Stwikey/alien-kitty/schematic/alienkitty.kicad_sch

## KiCad design schematic/alienkitty.kicad_sch (2026-06-14)

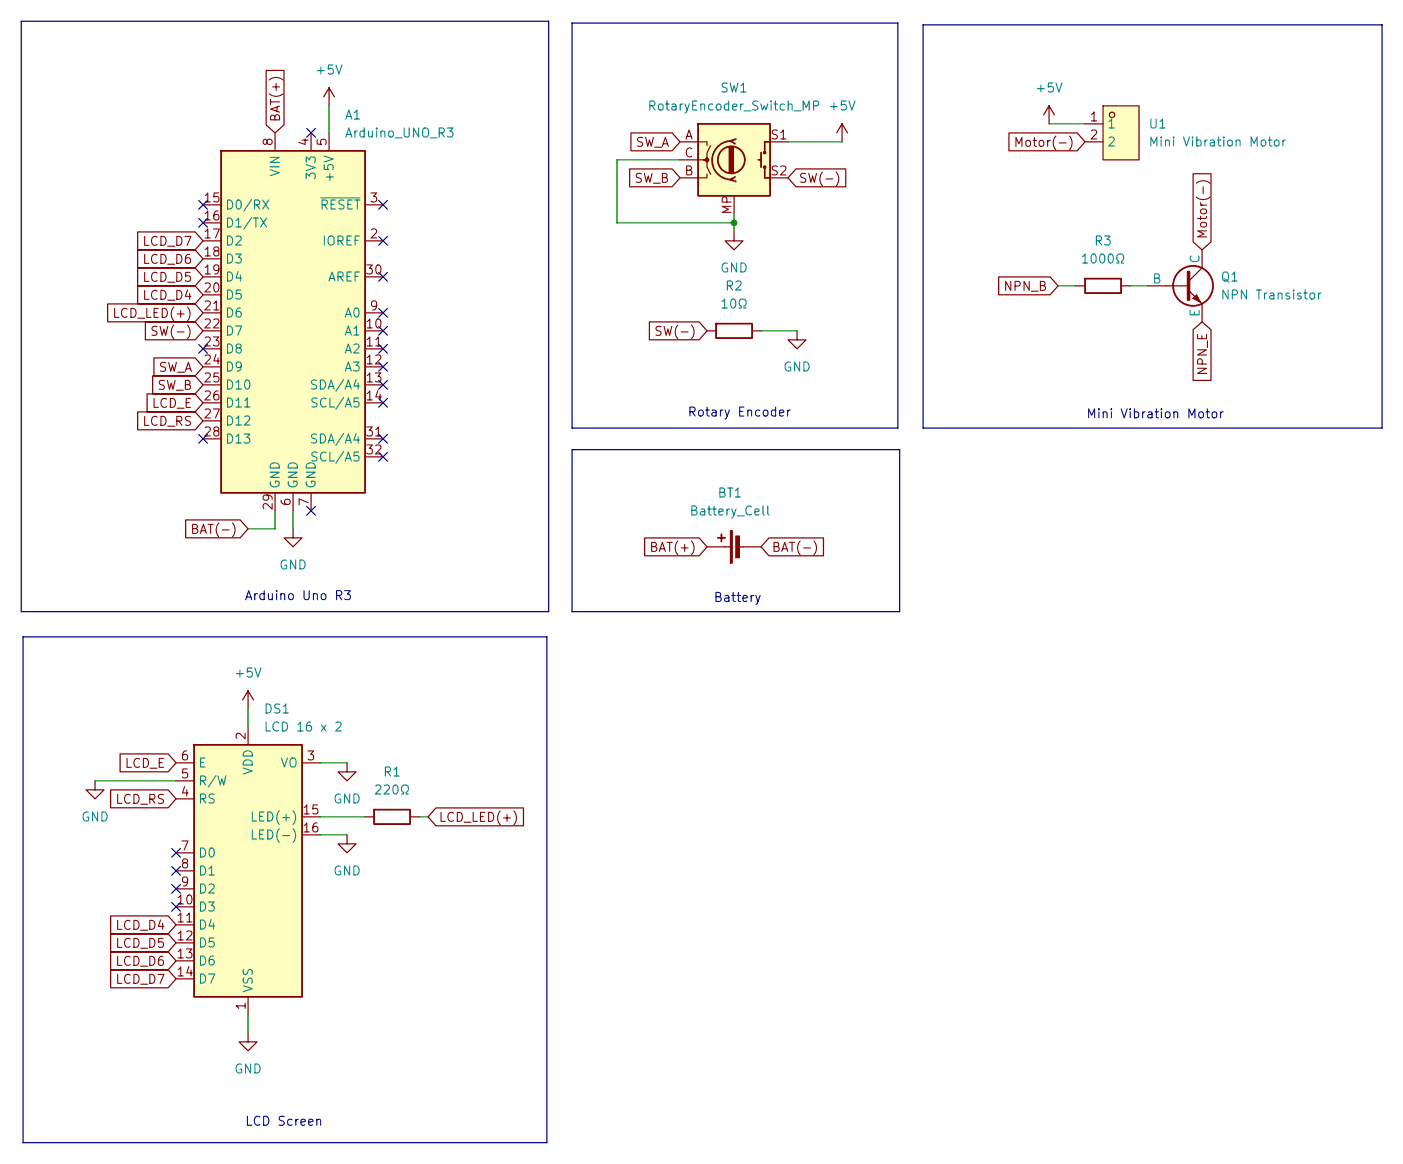
[picture p4: schematic alienkitty.kicad_sch]

Parts:
A1: Arduino_UNO_R3
BT1: Battery_Cell
DS1: LCD 16 x 2; WC1602A
Q1: NPN Transistor
R1: 220Ω
R2: 10Ω
R3: 1000Ω
SW1: RotaryEncoder_Switch_MP
U1: Mini Vibration Motor; VIBRATIONMOTOR-TH_LCM0827A3038F; MPN LCM0827A3038F; LCSC Part C2759981

Connections:
+5V: A1.5 (+5V), DS1.2 (VDD), SW1.S1, U1.1
BAT(+): A1.8 (VIN), BT1.1 (+)
BAT(-): A1.29 (GND), BT1.2 (-)
GND: A1.6 (GND), DS1.1 (VSS), DS1.3 (VO), DS1.5 (R/W), DS1.16 (LED(-)), R2.1, SW1.C, SW1.MP
LCD_D4: A1.20 (D5), DS1.11 (D4)
LCD_D5: A1.19 (D4), DS1.12 (D5)
LCD_D6: A1.18 (D3), DS1.13 (D6)
LCD_D7: A1.17 (D2), DS1.14 (D7)
LCD_E: A1.26 (D11), DS1.6 (E)
LCD_LED(+): A1.21 (D6), R1.1
LCD_RS: A1.27 (D12), DS1.4 (RS)
Motor(-): Q1.1 (C), U1.2
NPN_B: R3.2
NPN_E: Q1.3 (E)
unnamed: DS1.15 (LED(+)), R1.2
unnamed: Q1.2 (B), R3.1
SW(-): A1.22 (D7), R2.2, SW1.S2
SW_A: A1.24 (D9), SW1.A
SW_B: A1.25 (D10), SW1.B

Notes on the sheet:
LCD Screen
Mini Vibration Motor
Arduino Uno R3
Battery
Rotary Encoder
